WitzRed/humanoid-bike-rider/src/paper/assets/Built_robot3.jpg

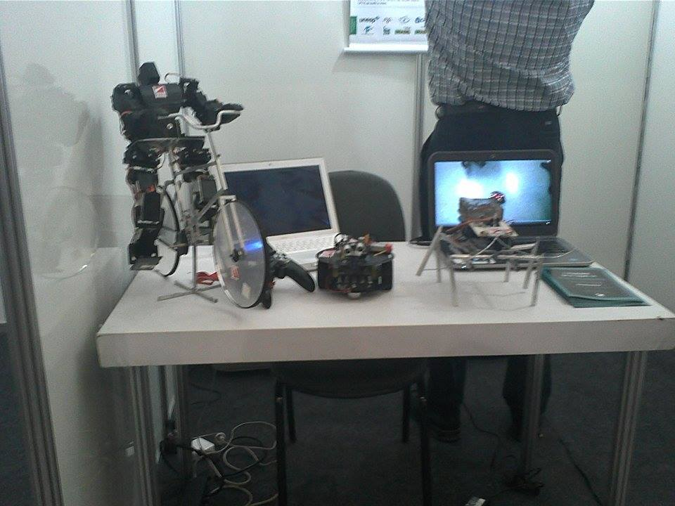
src/paper/assets/Built_robot3.jpg
