WitzRed/humanoid-bike-rider/src/paper/assets/Built_robot.jpg

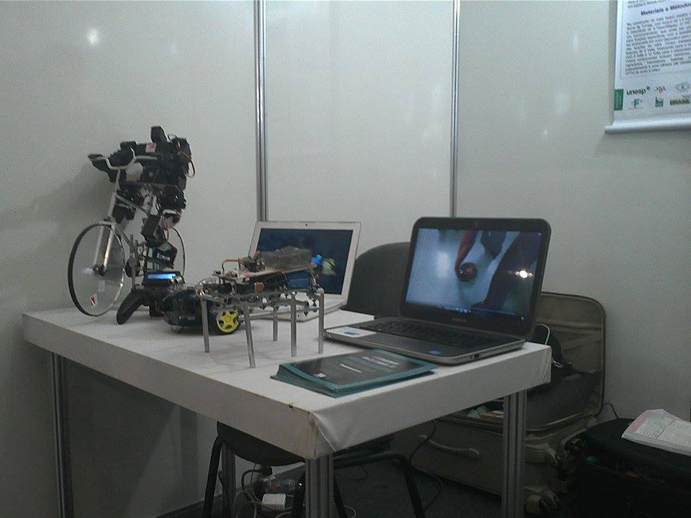
src/paper/assets/Built_robot.jpg
