WitzRed/humanoid-bike-rider/src/paper/assets/CAM00472.jpg

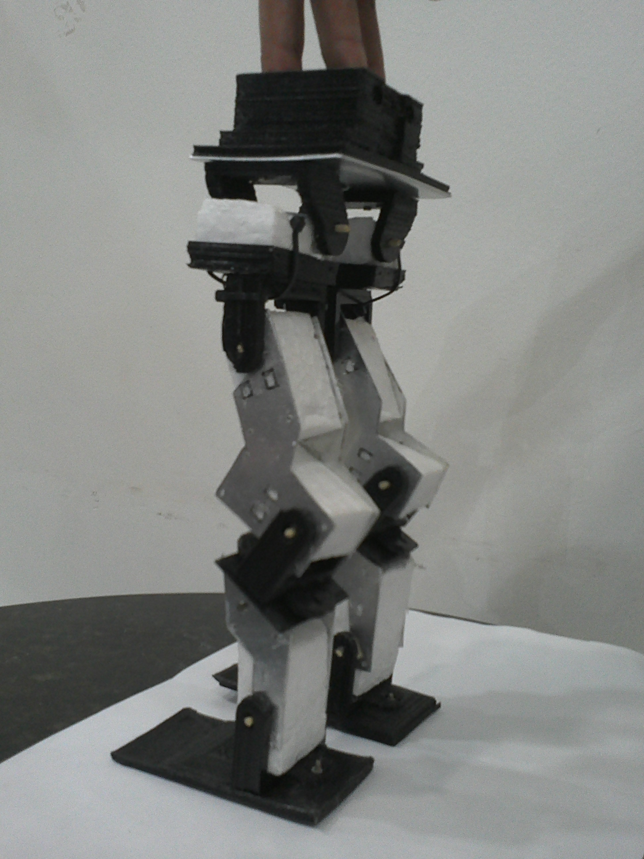
src/paper/assets/CAM00472.jpg
