WitzRed/humanoid-bike-rider/src/paper/assets/CAM00474.jpg

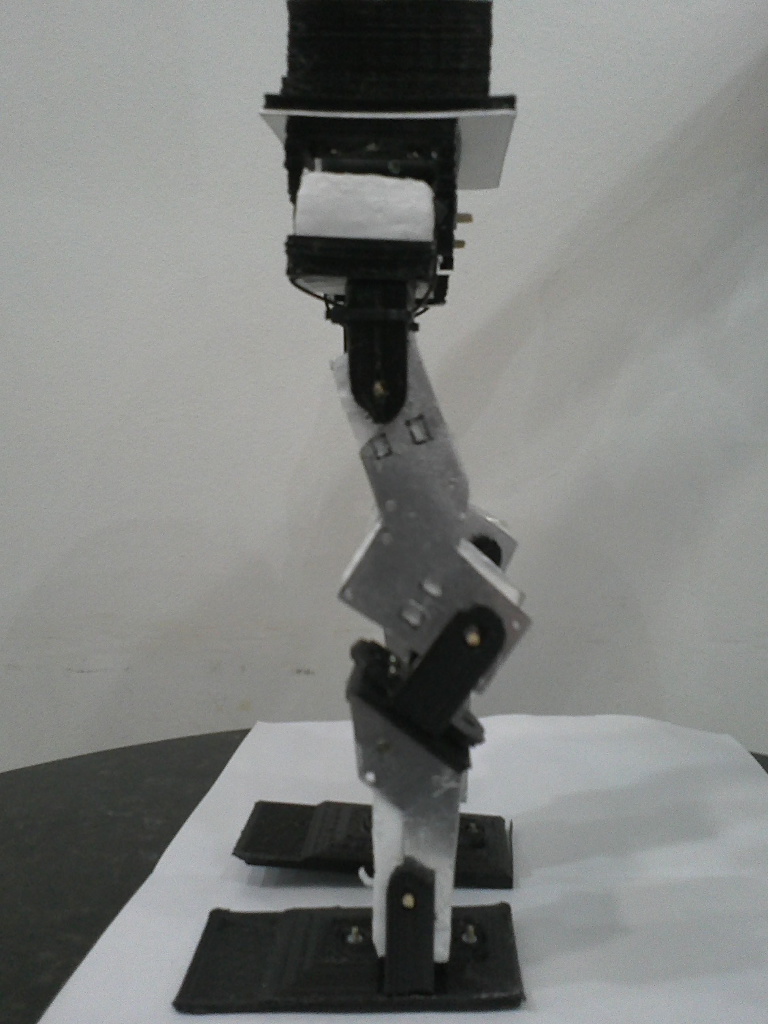
src/paper/assets/CAM00474.jpg
