WitzRed/humanoid-bike-rider/src/paper/assets/double.png

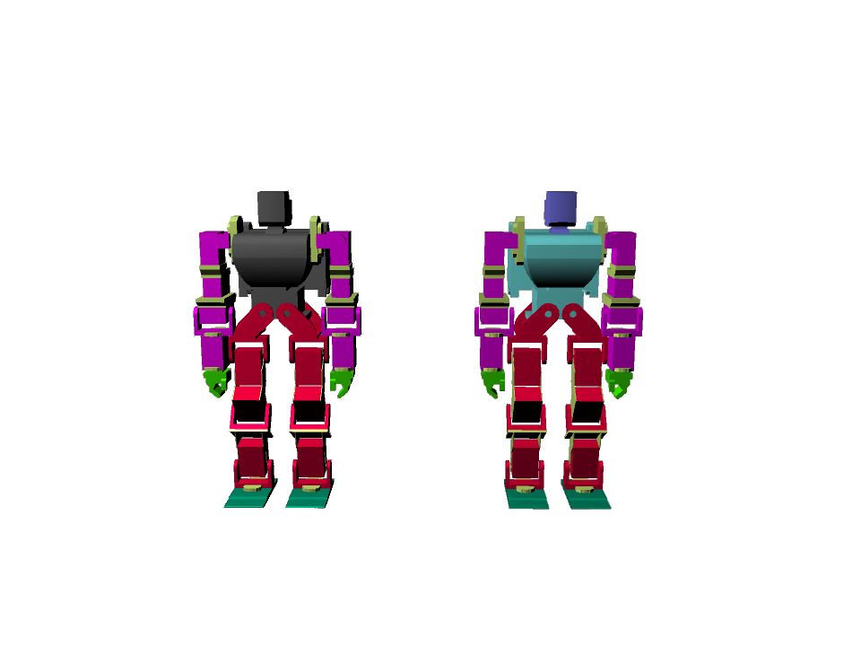
src/paper/assets/double.png
