WitzRed/humanoid-bike-rider/src/paper/assets/flowchart.png

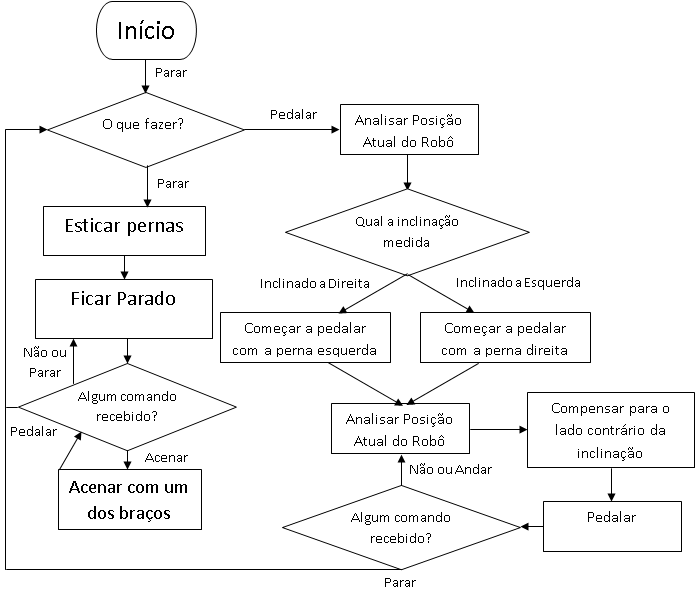
src/paper/assets/flowchart.png
