WitzRed/humanoid-bike-rider/src/paper/assets/robo_colorful2.png

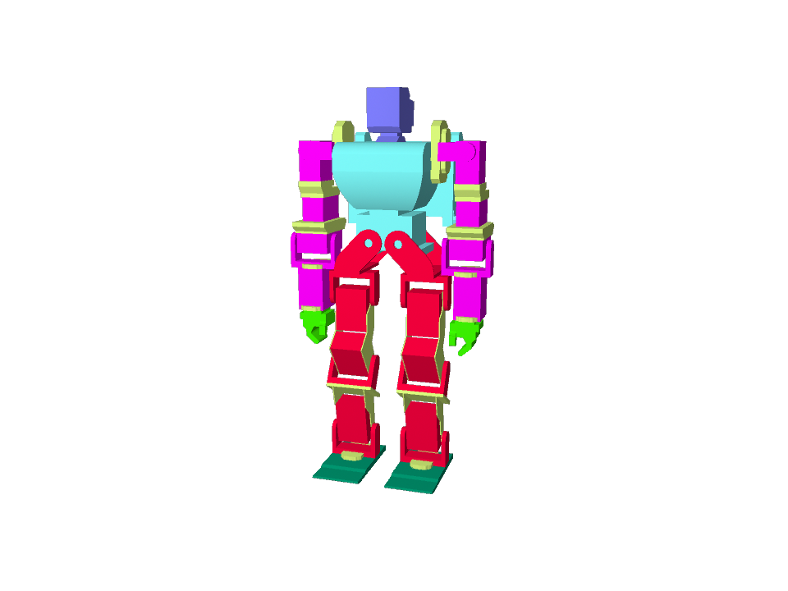
src/paper/assets/robo_colorful2.png
