WitzRed/humanoid-bike-rider/src/paper/assets/robo_colorful.png

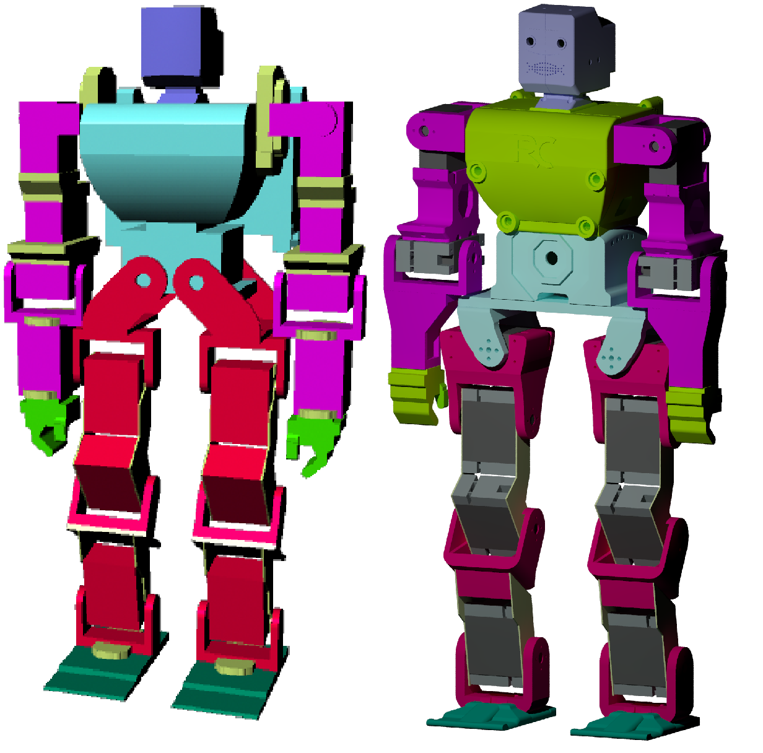
src/paper/assets/robo_colorful.png
