WitzRed/humanoid-bike-rider/src/paper/assets/ROBOT1.png

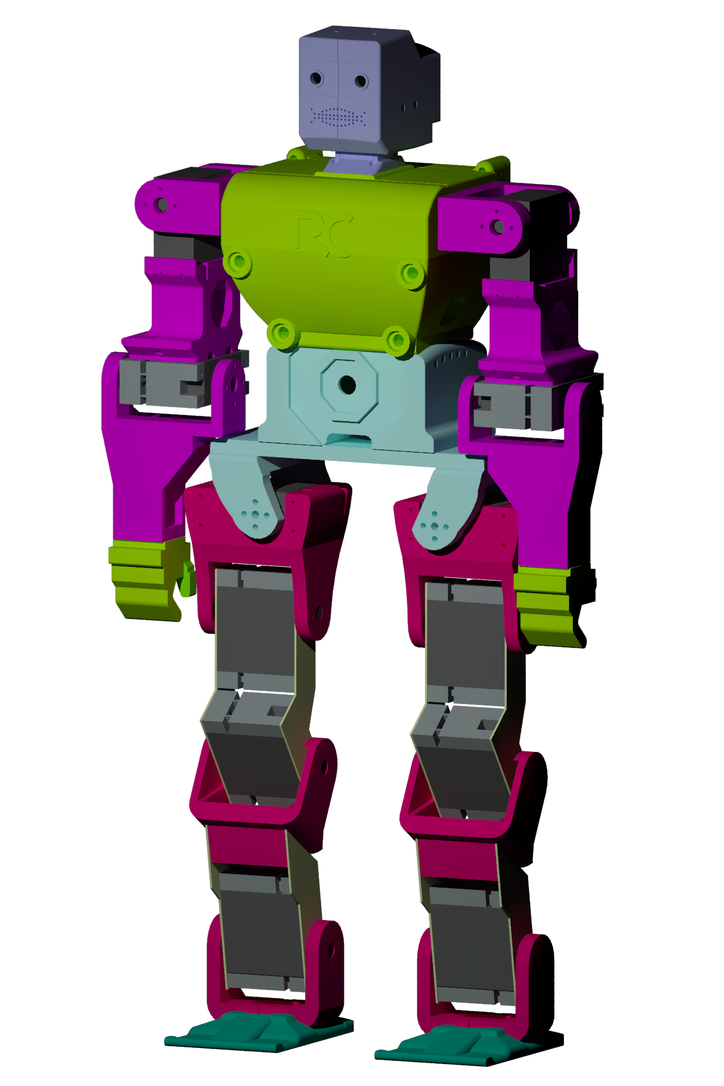
src/paper/assets/ROBOT1.png
