WitzRed/humanoid-bike-rider/src/paper/assets/robot2D.jpg

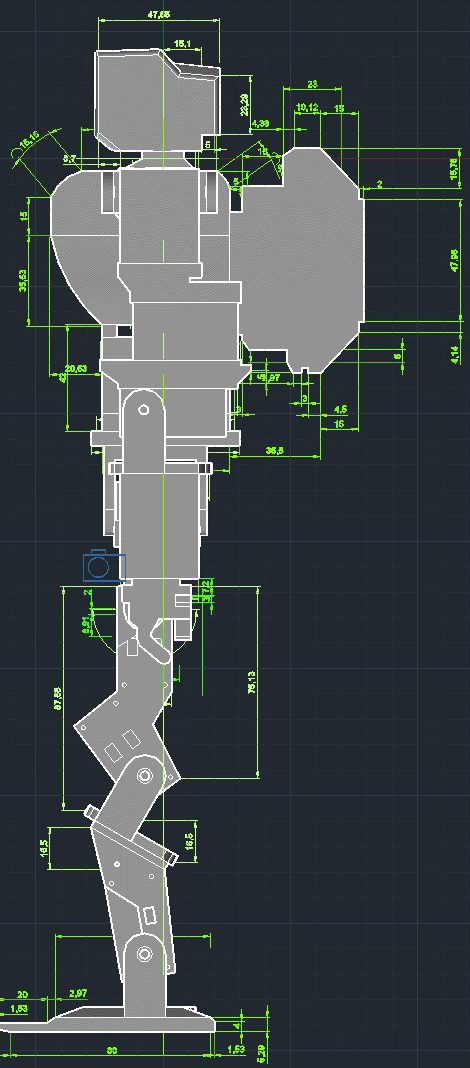
src/paper/assets/robot2D.jpg
