WitzRed/humanoid-bike-rider/src/paper/assets/two_neuron.jpg

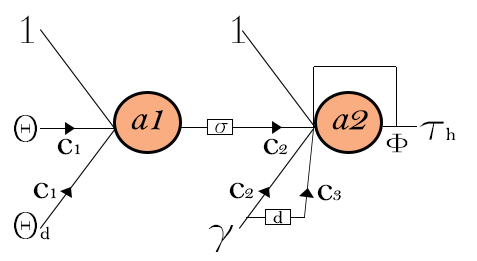
src/paper/assets/two_neuron.jpg
