WitzRed/humanoid-bike-rider/src/paper/assets/two_neuron_neat.jpg

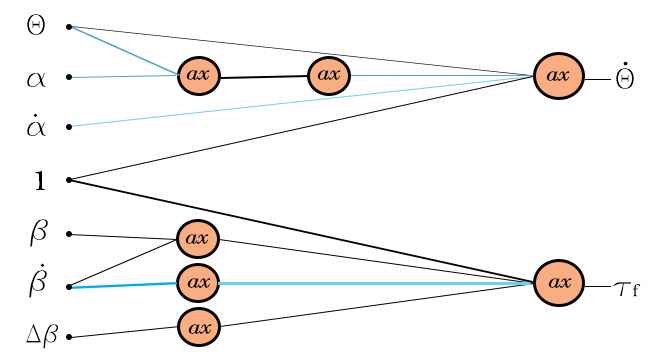
src/paper/assets/two_neuron_neat.jpg
