WitzRed/humanoid-bike-rider/src/3d-printing/PARTS_STL/BASE_NECK.stl

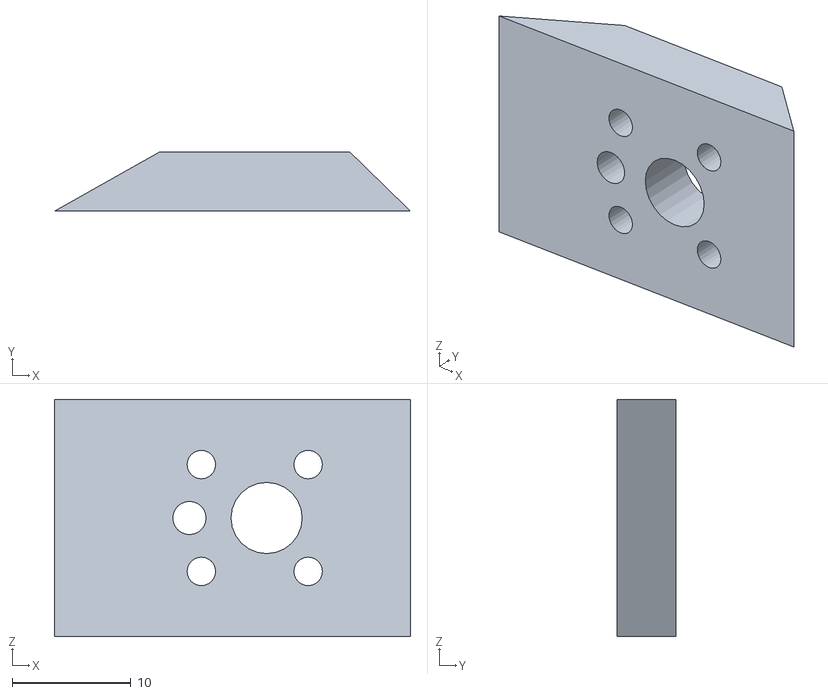
[picture p39: CAD file, 2022-11-03]
src/3d-printing/PARTS_STL/BASE_NECK.stl
30.0 x 5.00 x 20.0
