WitzRed/humanoid-bike-rider/src/3d-printing/PARTS_STL/BASE_ELBOW.stl

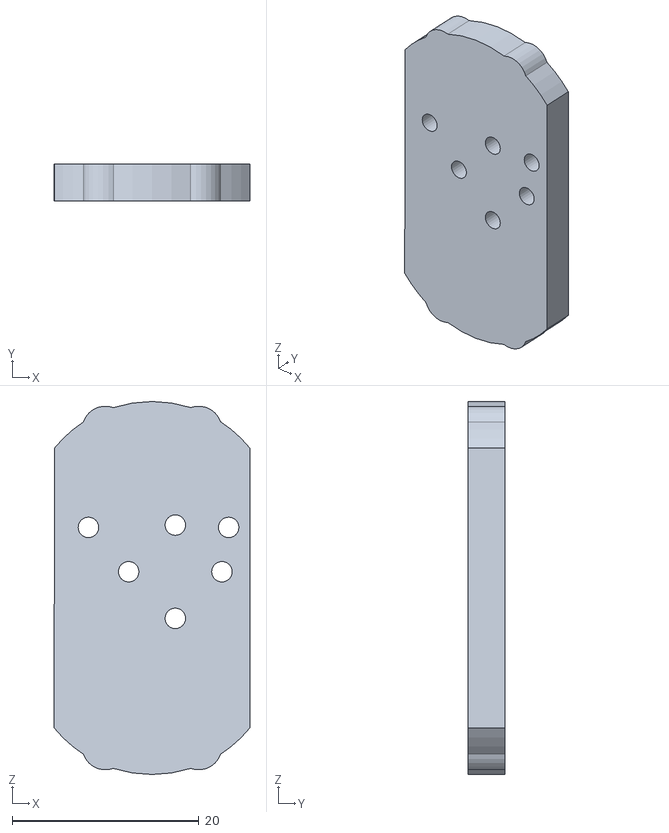
[picture p40: CAD file, 2022-11-03]
src/3d-printing/PARTS_STL/BASE_ELBOW.stl
21.0 x 4.00 x 40.0
