WitzRed/humanoid-bike-rider/src/3d-printing/PARTS_STL/BRACKET_WAIST.stl

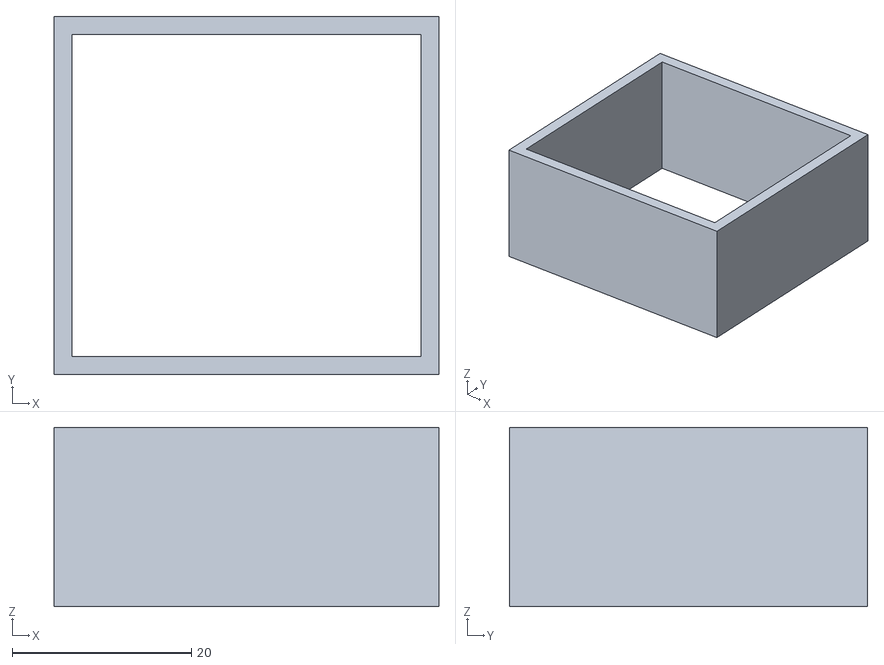
[picture p41: CAD file, 2022-11-03]
src/3d-printing/PARTS_STL/BRACKET_WAIST.stl
43.0 x 40.0 x 20.0
