WitzRed/humanoid-bike-rider/src/3d-printing/PARTS_STL/FINGER1.stl

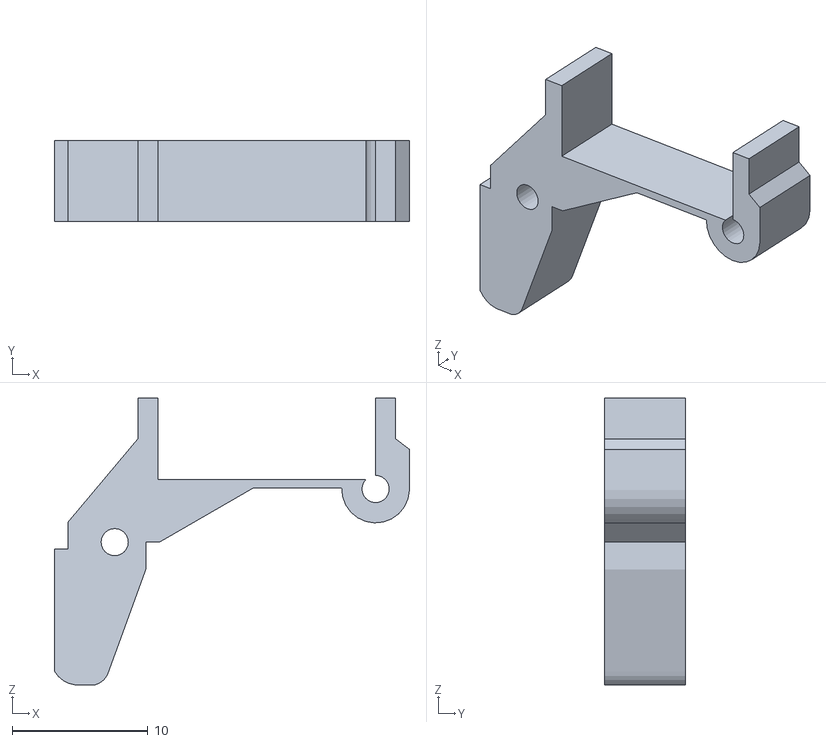
[picture p42: CAD file, 2022-11-03]
src/3d-printing/PARTS_STL/FINGER1.stl
26.2 x 6.00 x 21.1
