WitzRed/humanoid-bike-rider/src/3d-printing/PARTS_STL/BACK.stl

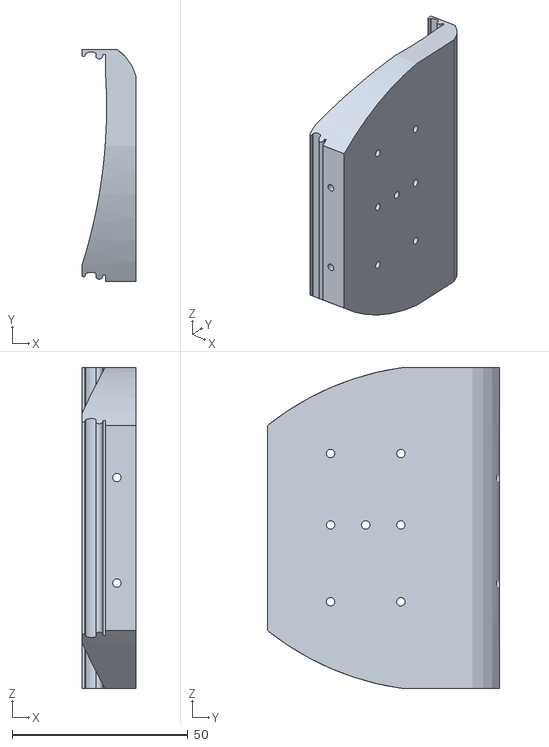
[picture p43: CAD file, 2022-11-03]
src/3d-printing/PARTS_STL/BACK.stl
15.5 x 66.0 x 91.3
