WitzRed/humanoid-bike-rider/src/3d-printing/PARTS_STL/BEARING_ANKLE.stl

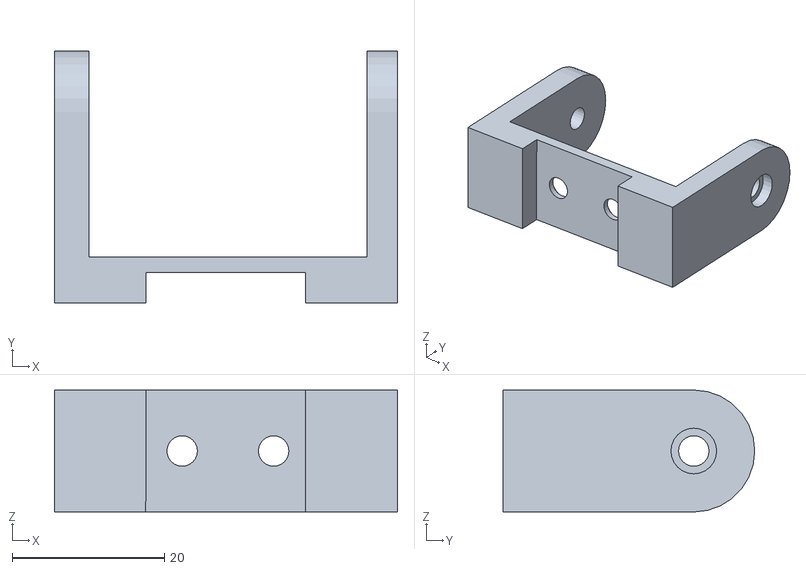
[picture p44: CAD file, 2022-11-03]
src/3d-printing/PARTS_STL/BEARING_ANKLE.stl
45.0 x 33.0 x 16.0
