WitzRed/humanoid-bike-rider/src/3d-printing/PARTS_STL/HEAD_E.stl

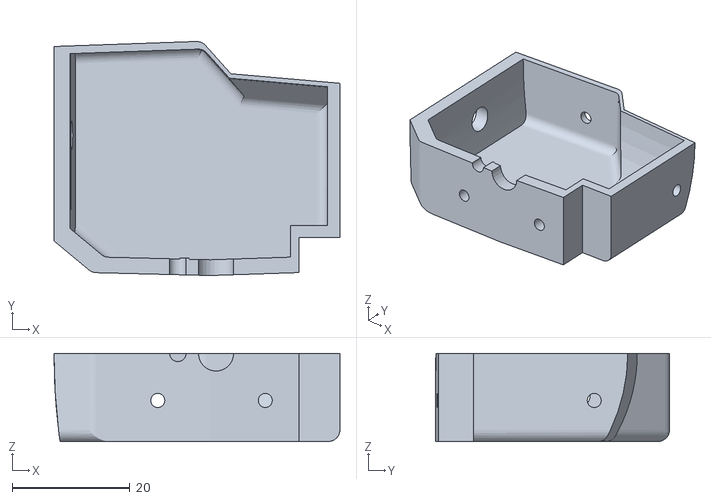
[picture p45: CAD file, 2022-11-03]
src/3d-printing/PARTS_STL/HEAD_E.stl
48.7 x 39.8 x 15.0
