WitzRed/humanoid-bike-rider/src/3d-printing/PARTS_STL/BASE_KNEE.stl

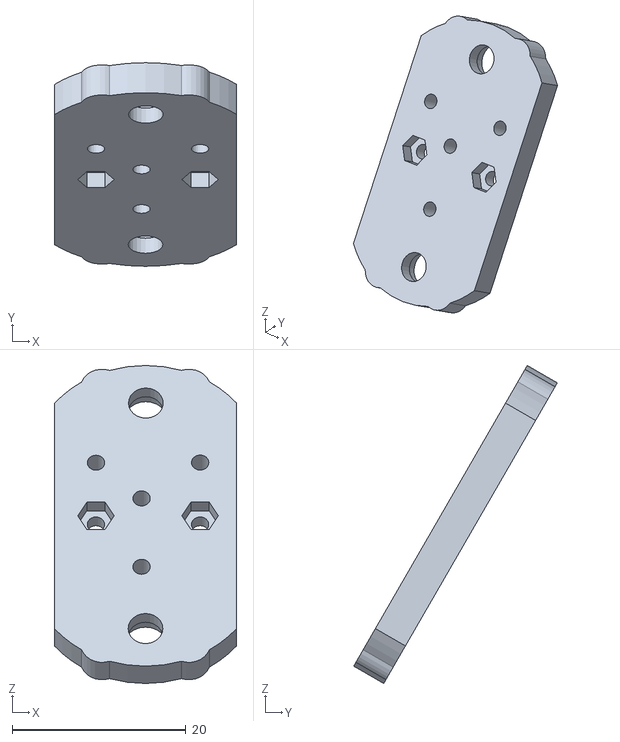
[picture p46: CAD file, 2022-11-03]
src/3d-printing/PARTS_STL/BASE_KNEE.stl
21.0 x 23.5 x 36.6
