WitzRed/humanoid-bike-rider/src/3d-printing/PARTS_STL/CHIN.stl

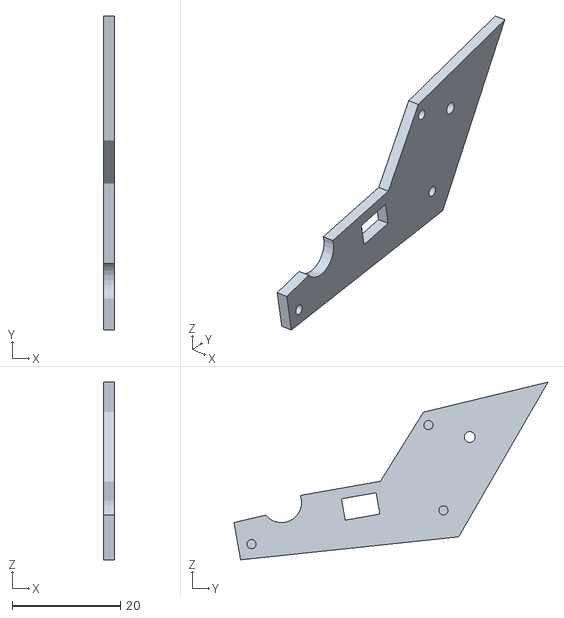
[picture p47: CAD file, 2022-11-03]
src/3d-printing/PARTS_STL/CHIN.stl
2.00 x 58.0 x 32.8
