WitzRed/humanoid-bike-rider/src/3d-printing/PARTS_STL/BATTERY_D.stl

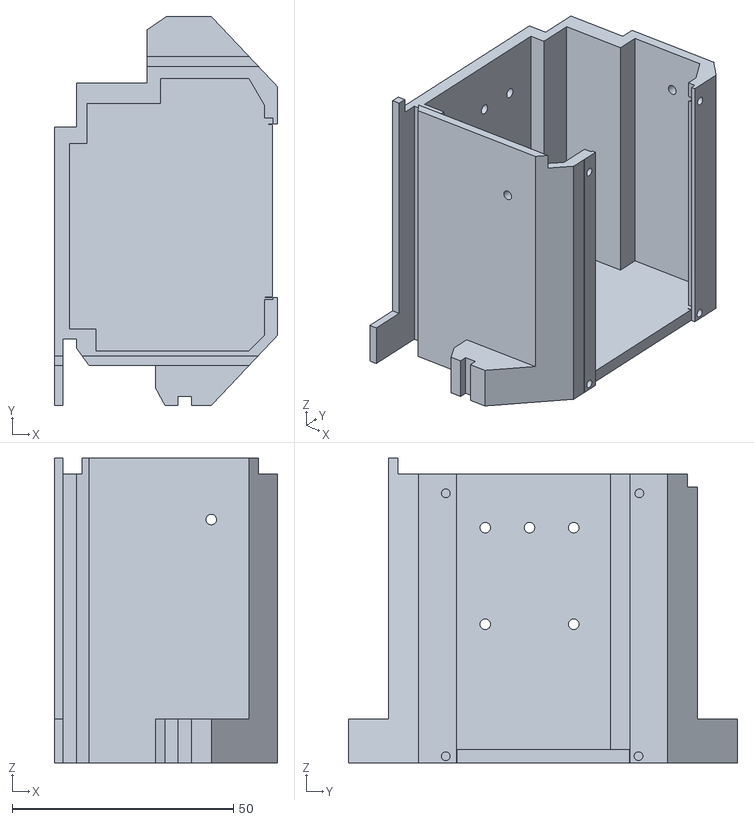
[picture p48: CAD file, 2022-11-03]
src/3d-printing/PARTS_STL/BATTERY_D.stl
50.5 x 88.0 x 69.0
