WitzRed/humanoid-bike-rider/src/3d-printing/PARTS_STL/FOREARM.stl

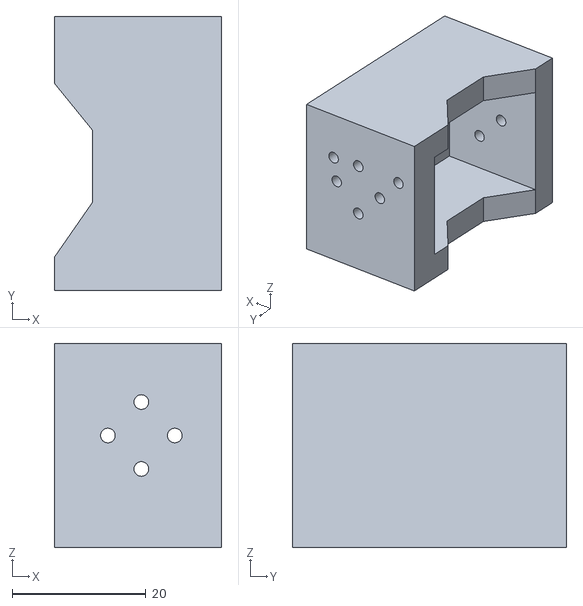
[picture p49: CAD file, 2022-11-03]
src/3d-printing/PARTS_STL/FOREARM.stl
25.0 x 41.0 x 30.5
