WitzRed/humanoid-bike-rider/src/3d-printing/PARTS_STL/FOOT_2.stl

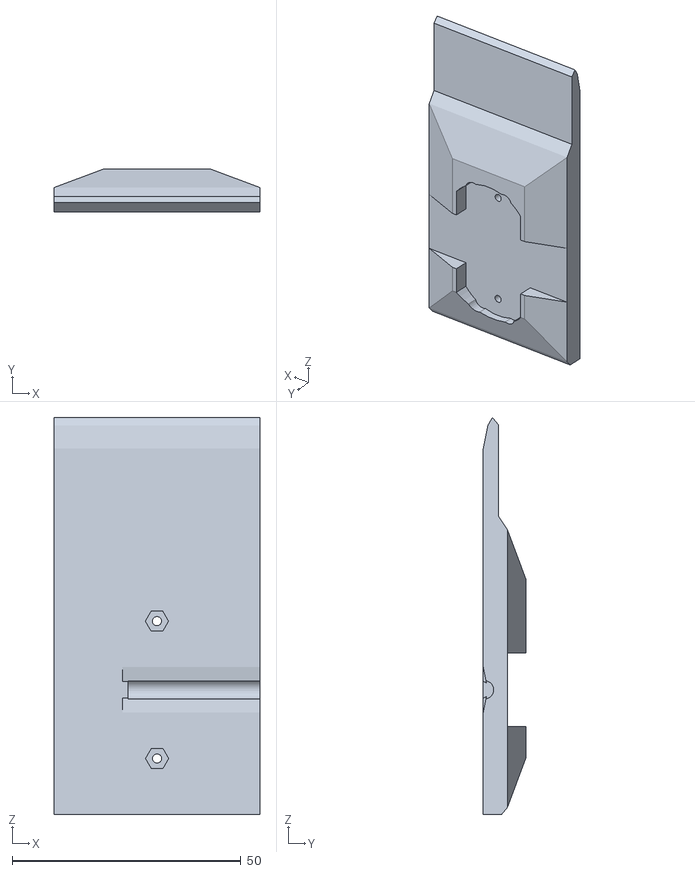
[picture p50: CAD file, 2022-11-03]
src/3d-printing/PARTS_STL/FOOT_2.stl
45.0 x 9.29 x 86.7
