WitzRed/humanoid-bike-rider/src/3d-printing/PARTS_STL/HIPS.stl

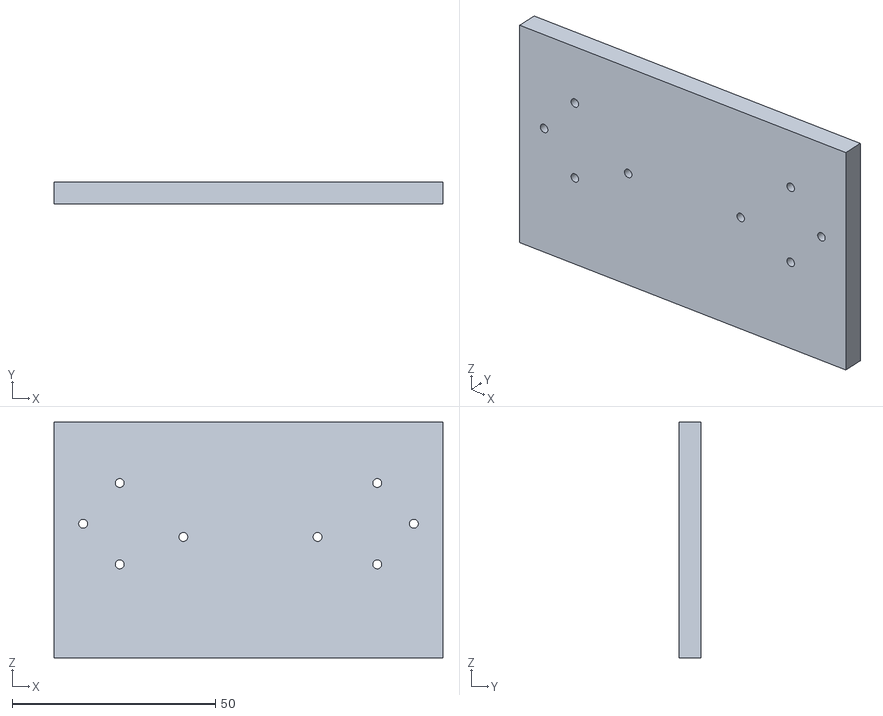
[picture p51: CAD file, 2022-11-03]
src/3d-printing/PARTS_STL/HIPS.stl
95.6 x 5.41 x 58.0
