WitzRed/humanoid-bike-rider/src/3d-printing/PARTS_STL/NEW_SHOLDER.stl

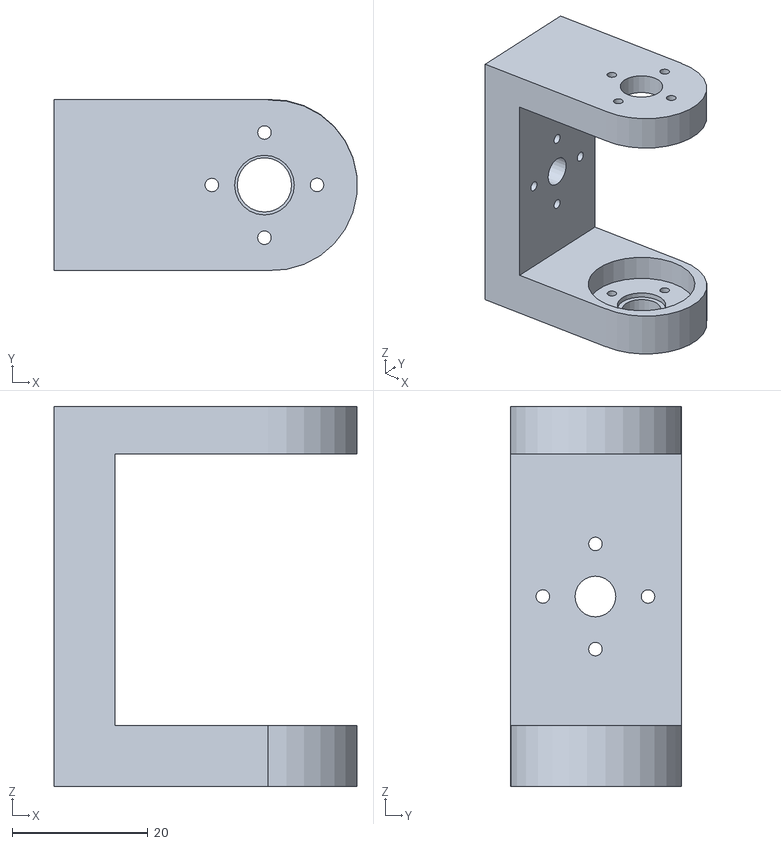
[picture p52: CAD file, 2022-11-03]
src/3d-printing/PARTS_STL/NEW_SHOLDER.stl
44.6 x 25.2 x 56.0
