WitzRed/humanoid-bike-rider/src/3d-printing/PARTS_STL/KNEE.stl

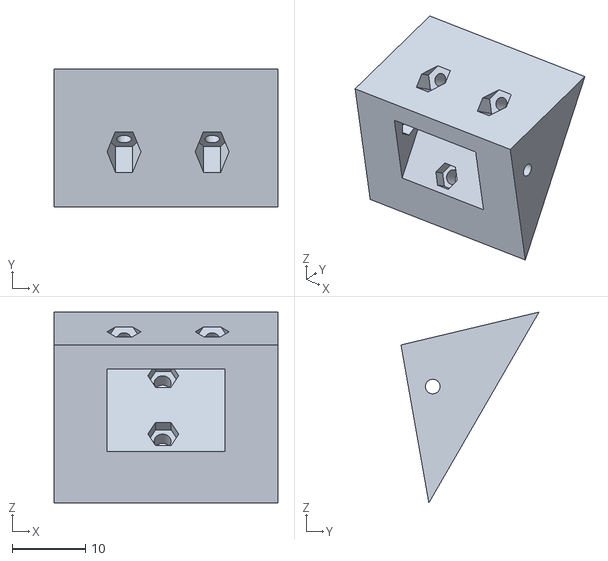
[picture p53: CAD file, 2022-11-03]
src/3d-printing/PARTS_STL/KNEE.stl
30.5 x 18.8 x 26.0
