WitzRed/humanoid-bike-rider/src/3d-printing/PARTS_STL/BASE_HIP.stl

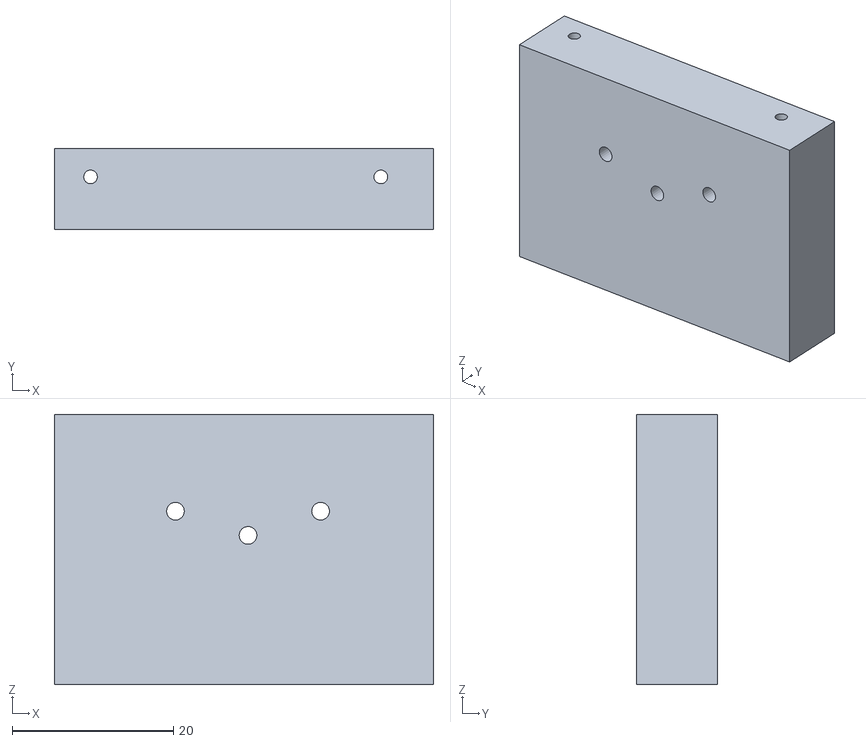
[picture p54: CAD file, 2022-11-03]
src/3d-printing/PARTS_STL/BASE_HIP.stl
47.0 x 10.00 x 33.5
