WitzRed/humanoid-bike-rider/src/3d-printing/PARTS_STL/CHEST.stl

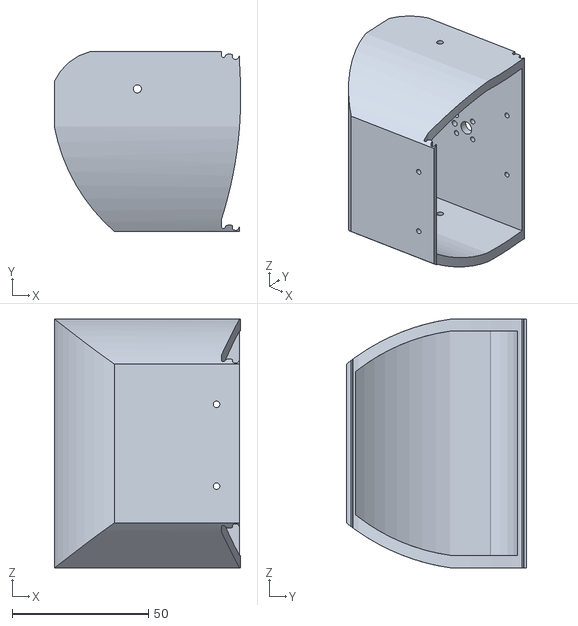
[picture p55: CAD file, 2022-11-03]
src/3d-printing/PARTS_STL/CHEST.stl
68.4 x 66.0 x 91.3
