WitzRed/humanoid-bike-rider/src/3d-printing/PARTS_STL/BATTERY_E.stl

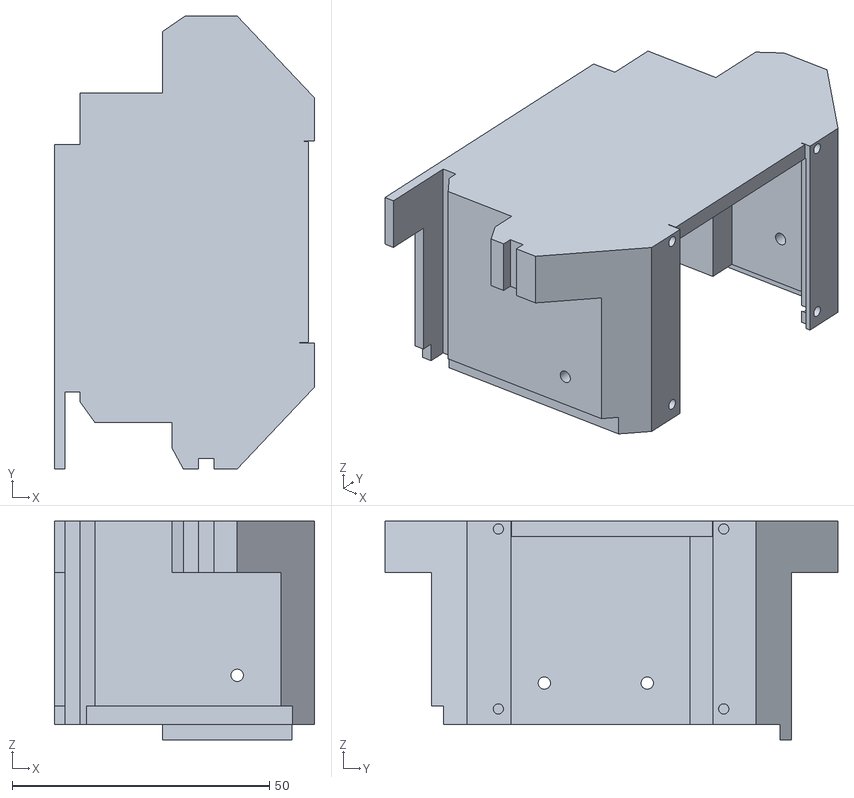
[picture p56: CAD file, 2022-11-03]
src/3d-printing/PARTS_STL/BATTERY_E.stl
50.5 x 88.0 x 42.5
