WitzRed/humanoid-bike-rider/src/3d-printing/PARTS_STL/THIGH.stl

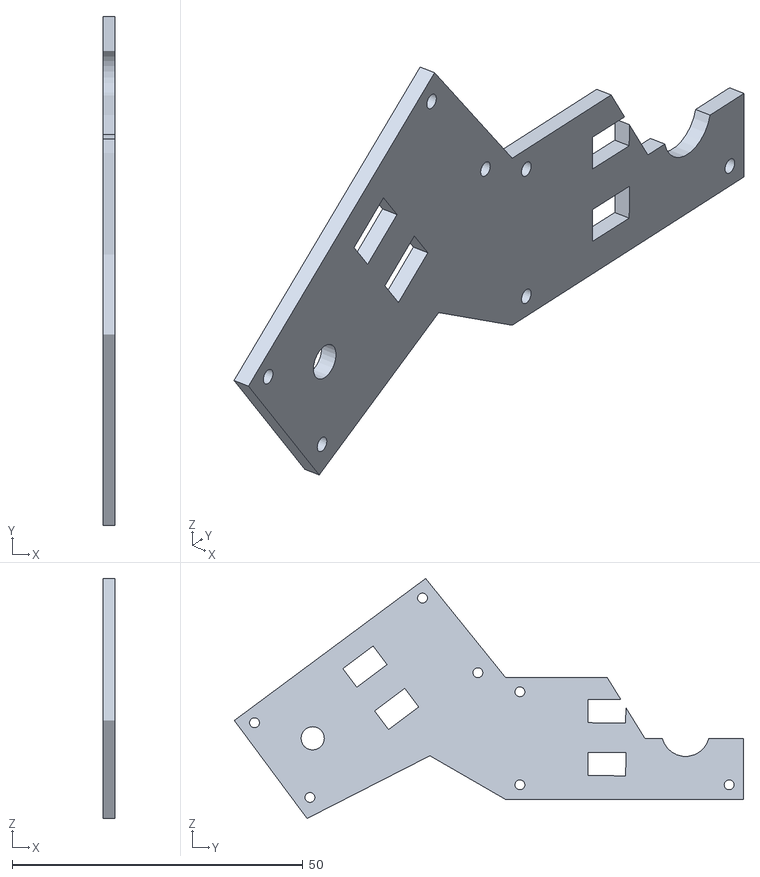
[picture p57: CAD file, 2022-11-03]
src/3d-printing/PARTS_STL/THIGH.stl
2.00 x 87.6 x 41.3
