WitzRed/humanoid-bike-rider/src/3d-printing/PARTS_STL/WAIST_TOP.stl

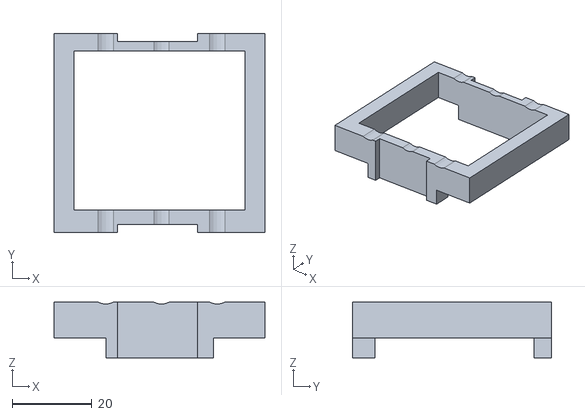
[picture p58: CAD file, 2022-11-03]
src/3d-printing/PARTS_STL/WAIST_TOP.stl
53.0 x 50.0 x 14.0
