WitzRed/humanoid-bike-rider/src/paper/assets/printing3D.jpg

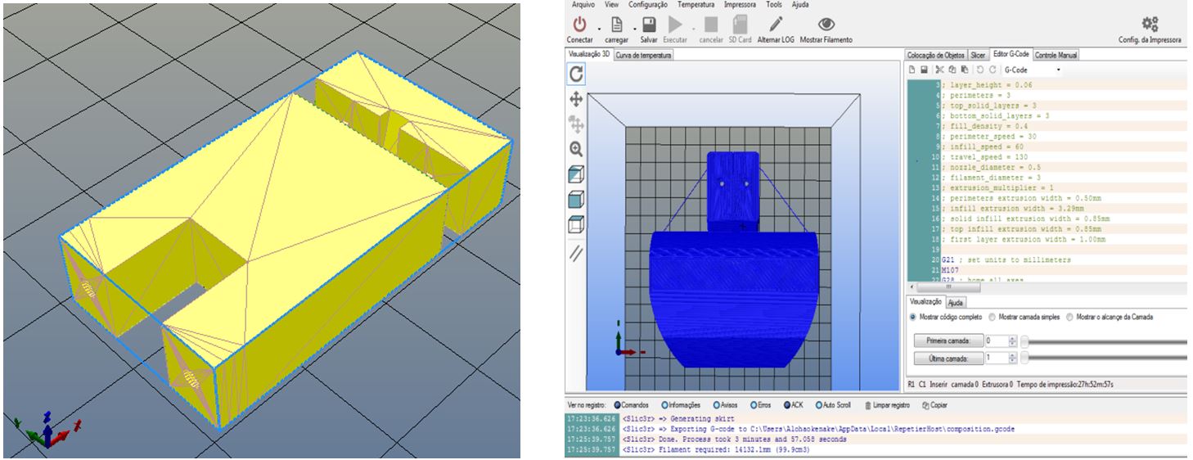
src/paper/assets/printing3D.jpg
